blanboom/NixieClock/Firmware/STC15/EEPROM.c

//	本程序是STC系列的内置EEPROM读写程序。

#include "config.h"
#include "eeprom.h"


//========================================================================
// 函数: void	ISP_Disable(void)
// 描述: 禁止访问ISP/IAP.
// 参数: non.
// 返回: non.
// 版本: V1.0, 2012-10-22
//========================================================================
void	DisableEEPROM(void)
{
	ISP_CONTR = 0;			//禁止ISP/IAP操作
	ISP_CMD   = 0;			//去除ISP/IAP命令
	ISP_TRIG  = 0;			//防止ISP/IAP命令误触发
	ISP_ADDRH = 0xff;		//清0地址高字节
	ISP_ADDRL = 0xff;		//清0地址低字节，指向非EEPROM区，防止误操作
}

//========================================================================
// 函数: void EEPROM_read_n(u16 EE_address,u8 *DataAddress,u16 number)
// 描述: 从指定EEPROM首地址读出n个字节放指定的缓冲.
// 参数: EE_address:  读出EEPROM的首地址.
//       DataAddress: 读出数据放缓冲的首地址.
//       number:      读出的字节长度.
// 返回: non.
// 版本: V1.0, 2012-10-22
//========================================================================

void EEPROM_read_n(u16 EE_address,u8 *DataAddress,u16 number)
{
	EA = 0;		//禁止中断
	ISP_CONTR = (ISP_EN + ISP_WAIT_FREQUENCY);	//设置等待时间，允许ISP/IAP操作，送一次就够
	ISP_READ();									//送字节读命令，命令不需改变时，不需重新送命令
	do
	{
		ISP_ADDRH = EE_address / 256;		//送地址高字节（地址需要改变时才需重新送地址）
		ISP_ADDRL = EE_address % 256;		//送地址低字节
		ISP_TRIG();							//先送5AH，再送A5H到ISP/IAP触发寄存器，每次都需要如此
											//送完A5H后，ISP/IAP命令立即被触发启动
											//CPU等待IAP完成后，才会继续执行程序。
		_nop_();
		*DataAddress = ISP_DATA;			//读出的数据送往
		EE_address++;
		DataAddress++;
	}while(--number);

	DisableEEPROM();
	EA = 1;		//重新允许中断
}


/******************** 扇区擦除函数 *****************/
//========================================================================
// 函数: void EEPROM_SectorErase(u16 EE_address)
// 描述: 把指定地址的EEPROM扇区擦除.
// 参数: EE_address:  要擦除的扇区EEPROM的地址.
// 返回: non.
// 版本: V1.0, 2013-5-10
//========================================================================
void EEPROM_SectorErase(u16 EE_address)
{
	EA = 0;		//禁止中断
											//只有扇区擦除，没有字节擦除，512字节/扇区。
											//扇区中任意一个字节地址都是扇区地址。
	ISP_ADDRH = EE_address / 256;			//送扇区地址高字节（地址需要改变时才需重新送地址）
	ISP_ADDRL = EE_address % 256;			//送扇区地址低字节
	ISP_CONTR = (ISP_EN + ISP_WAIT_FREQUENCY);	//设置等待时间，允许ISP/IAP操作，送一次就够
	ISP_ERASE();							//送扇区擦除命令，命令不需改变时，不需重新送命令
	ISP_TRIG();
	_nop_();
	DisableEEPROM();
	EA = 1;		//重新允许中断
}

//========================================================================
// 函数: void EEPROM_write_n(u16 EE_address,u8 *DataAddress,u16 number)
// 描述: 把缓冲的n个字节写入指定首地址的EEPROM.
// 参数: EE_address:  写入EEPROM的首地址.
//       DataAddress: 写入源数据的缓冲的首地址.
//       number:      写入的字节长度.
// 返回: non.
// 版本: V1.0, 2012-10-22
//========================================================================
void EEPROM_write_n(u16 EE_address,u8 *DataAddress,u16 number)
{
	EA = 0;		//禁止中断

	ISP_CONTR = (ISP_EN + ISP_WAIT_FREQUENCY);	//设置等待时间，允许ISP/IAP操作，送一次就够
	ISP_WRITE();							//送字节写命令，命令不需改变时，不需重新送命令
	do
	{
		ISP_ADDRH = EE_address / 256;		//送地址高字节（地址需要改变时才需重新送地址）
		ISP_ADDRL = EE_address % 256;		//送地址低字节
		ISP_DATA  = *DataAddress;			//送数据到ISP_DATA，只有数据改变时才需重新送
		ISP_TRIG();
		_nop_();
		EE_address++;
		DataAddress++;
	}while(--number);

	DisableEEPROM();
	EA = 1;		//重新允许中断
}
