blanboom/NixieClock/Firmware/App/TImeUpdate.h

/**
 * 时间更新相关函数
 * 作者：    Blanboom
 * 最后更新：2014-07-21
 * http://blanboom.org
 **************************
 * 使用时应根据时钟频率调整定时器初值
 */
 
#ifndef __TIME_UPDATE_H
#define __TIME_UPDATE_H

#include "config.h"

void timerInit(void);
void timeUpdate_ISR(void);

#endif
