blanboom/NixieClock/Firmware/STC15/EEPROM.h

#ifndef	__EEPROM_H
#define	__EEPROM_H

#include	"config.h"

//	选择MCU型号
#define	MCU_Type	STC15F_L2K08S2	//STC15F_L2K08S2, STC15F_L2K16S2, STC15F_L2K24S2, STC15F_L2K32S2, STC15F_L2K40S2, STC15F_L2K48S2, STC15F_L2K56S2, STC15F_L2K60S2, IAP15F_L2K61S2


/************************** ISP/IAP *****************************
 IAP系列 可以在应用程序修改应用程序。

STC15F/L2KxxS2	扇区分配，512字节/扇区，从0x0000开始。

     型号        大小   扇区数  开始地址  结束地址   MOVC读偏移地址
STC15F/L2K08S2   53K   106扇区  0x0000  ~  0xD3FF        0x2000
STC15F/L2K16S2   45K    90扇区  0x0000  ~  0xB3FF        0x4000
STC15F/L2K24S2   37K    74扇区  0x0000  ~  0x93FF        0x6000
STC15F/L2K32S2   29K    58扇区  0x0000  ~  0x73FF        0x8000
STC15F/L2K40S2   21K    42扇区  0x0000  ~  0x53FF        0xA000
STC15F/L2K48S2   13K    26扇区  0x0000  ~  0x33FF        0xC000
STC15F/L2K56S2   5K     10扇区  0x0000  ~  0x13FF        0xE000
STC15F/L2K60S2   1K      2扇区  0x0000  ~  0x03FF        0xF000

STC15F/L2K61S2   无EPROM, 整个122扇区的FLASH都可以擦写 地址 0x0000~0xF3ff.

*/

#if   (MCU_Type == STC15F_L2K08S2)
      #define   MOVC_ShiftAddress    0x2000
#elif (MCU_Type == STC15F_L2K16S2)
      #define   MOVC_ShiftAddress    0x4000
#elif (MCU_Type == STC15F_L2K24S2
      #define   MOVC_ShiftAddress    0x6000
#elif (MCU_Type == STC15F_L2K32S2
      #define   MOVC_ShiftAddress    0x8000
#elif (MCU_Type == STC15F_L2K40S2
      #define   MOVC_ShiftAddress    0xA000
#elif (MCU_Type == STC15F_L2K48S2
      #define   MOVC_ShiftAddress    0xC000
#elif (MCU_Type == STC15F_L2K56S2
      #define   MOVC_ShiftAddress    0xE000
#elif (MCU_Type == STC15F_L2K60S2
      #define   MOVC_ShiftAddress    0xF000
#elif (MCU_Type == IAP15F_L2K61S2
      #define   MOVC_ShiftAddress    0x0000
#endif


void	DisableEEPROM(void);
void 	EEPROM_read_n(u16 EE_address,u8 *DataAddress,u16 number);
void 	EEPROM_write_n(u16 EE_address,u8 *DataAddress,u16 number);
void	EEPROM_SectorErase(u16 EE_address);


#endif
